bittailor/BtSolarMonitor/Firmware/sketchbook/SolarMonitor/SolarMonitorSettings.default_settings.hpp

Bt::SolarMonitor::MainController::Settings sSettings = {
         {
                  "GprsSimPin",
                  "GprsAccessPointName"
         },
         {
                  "MqttBroker",
                  "MqttDeviceId",
                  "MqttUser",
                  "MqttPassword"
         }
};
