bittailor/BtSolarMonitor/Firmware/sketchbook/SleepAndWakeupWithTC/SleepAndWakeupWithTC.ino

#include <Arduino.h>

// Connect a terminal to Serial (D0/D1), or define this as SerialUSB
#define mySerial Serial

volatile bool TC3_flag = false;
volatile uint32_t tc3_millis = 0;

void configureTC3a();

void setup()
{
    delay(3000);

    pinMode(LED_BUILTIN, OUTPUT);

    mySerial.begin(57600);
    mySerial.println("Startup");

    configureTC3a();

    mySerial.println("Configuration Complete");
}

void loop()
{
    if (TC3_flag) {
        static int counter;
        static uint32_t prev_millis;
        uint32_t my_millis = tc3_millis;
        TC3_flag = false;
        mySerial.println(String("tick, ms: ") + (my_millis - prev_millis) + " " + counter);
        prev_millis = my_millis;
        flashLED();
        if (++counter >= 60) {
            static uint32_t prev_millis;
            mySerial.println(String("Long term tick: ") + (my_millis - prev_millis));
            prev_millis = my_millis;
            counter = 0;
        }
    }
    systemSleep();
}

void flashLED()
{
    static bool led;
    led = !led;                         //flip status led
    if (led) {
        digitalWrite(LED_BUILTIN, LOW);
    }
    else {
        digitalWrite(LED_BUILTIN, HIGH);
    }
}

void systemSleep()
{
    // Set the sleep mode
    SCB->SCR |= SCB_SCR_SLEEPDEEP_Msk;

    if (USB->DEVICE.FSMSTATUS.bit.FSMSTATE == USB_FSMSTATUS_FSMSTATE_SUSPEND_Val) {
        // Disable USB
        USBDevice.detach();

        // SAMD sleep
        __WFI();

        // Enable USB and wait for resume if attached
        USBDevice.attach();
        USB->DEVICE.CTRLB.bit.UPRSM = 0x01u;
        while (USB->DEVICE.CTRLB.bit.UPRSM)
            ;
    }
}

void configureTC3a()
{
    // The GCLK clock provider to use
    // GCLK0, GCLK1 & GCLK3 are used already, see startup.c
    const uint8_t GCLK_SRC = 4;

    // Configure the XOSC32K to run in standby
    SYSCTRL->XOSC32K.bit.RUNSTDBY = 1;

    // Setup clock provider GCLK_SRC with a /2 source divider
    // GCLK_GENDIV_ID(X) specifies which GCLK we are configuring
    // GCLK_GENDIV_DIV(Y) specifies the clock prescalar / divider
    // If GENCTRL.DIVSEL is set (see further below) the divider
    // is 2^(Y+1). If GENCTRL.DIVSEL is 0, the divider is simply Y
    // This register has to be written in a single operation
    GCLK->GENDIV.reg = GCLK_GENDIV_ID(GCLK_SRC) | GCLK_GENDIV_DIV(2);
    while ( GCLK->STATUS.reg & GCLK_STATUS_SYNCBUSY) {
        /* Wait for synchronization */
    }

    // Configure the GCLK module
    // GCLK_GENCTRL_GENEN, enable the specific GCLK module
    // GCLK_GENCTRL_SRC_XOSC32K, set the source to the XOSC32K
    // GCLK_GENCTRL_ID(X), specifies which GCLK we are configuring
    // GCLK_GENCTRL_DIVSEL, specify which prescalar mode we are using
    // GCLK_RUNSTDBY, keep the GCLK running when in standby mode
    // Output from this module is 16khz (32khz / 2)
    // This register has to be written in a single operation.
    GCLK->GENCTRL.reg = GCLK_GENCTRL_GENEN |
            GCLK_GENCTRL_SRC_XOSC32K |
            GCLK_GENCTRL_ID(GCLK_SRC) |
            GCLK_GENCTRL_RUNSTDBY;
    while (GCLK->STATUS.reg & GCLK_STATUS_SYNCBUSY) {
        /* Wait for synchronization */
    }

    // Turn the power to the TC3 module on
    PM->APBCMASK.reg |= PM_APBCMASK_TC3;

    // Set TC3 (shared with TCC2) GCLK source to GCLK_SRC
    // GCLK_CLKCTRL_CLKEN, enable the generic clock
    // GCLK_CLKCTRL_GEN(X), specifies the GCLK generator source
    // GCLK_CLKCTRL_ID(X), specifies which generic clock we are configuring
    GCLK->CLKCTRL.reg = GCLK_CLKCTRL_CLKEN |
            GCLK_CLKCTRL_GEN(GCLK_SRC) |
            GCLK_CLKCTRL_ID(GCM_TCC2_TC3);
    while (GCLK->STATUS.reg & GCLK_STATUS_SYNCBUSY) {
        /* Wait for synchronization */
    }

    // Disable TC3. This is required (if enabled already)
    // before setting certain registers
    TC3->COUNT8.CTRLA.reg &= ~TC_CTRLA_ENABLE;
    while (TC3->COUNT8.STATUS.reg & TC_STATUS_SYNCBUSY) {
        /* Wait for synchronization */
    }

    // Set the mode to 8 bit and set it to run in standby
    // TC_CTRLA_MODE_COUNT8, specify 8bit mode
    // TC_CTRLA_RUNSTDBY, keep the module running when in standby
    // TC_CTRLA_PRESCALER_DIVxx, set the prescalar to 64
    // Prescalar options include: DIV1, DIV2, DIV4, DIV8,
    // DIV16, DIV64, DIV256, DIV1024
    TC3->COUNT8.CTRLA.reg = TC_CTRLA_MODE_COUNT8 |
            TC_CTRLA_RUNSTDBY |
            TC_CTRLA_PRESCALER_DIV64;
    while (TC3->COUNT8.STATUS.reg & TC_STATUS_SYNCBUSY) {
        /* Wait for synchronization */
    }

    // Enable interrupt on overflow
    // TC_INTENSET_OVF, enable an interrupt on overflow
    TC3->COUNT8.INTENSET.reg = TC_INTENSET_OVF;
    while (TC3->COUNT8.STATUS.reg & TC_STATUS_SYNCBUSY) {
        /* Wait for synchronization */
    }

    // Enable TC3
    TC3->COUNT8.CTRLA.reg |= TC_CTRLA_ENABLE;
    while (TC3->COUNT8.STATUS.reg & TC_STATUS_SYNCBUSY) {
        /* Wait for synchronization */
    }

    // Enable the TC3 interrupt vector
    // Set the priority to max
    NVIC_EnableIRQ(TC3_IRQn);
    NVIC_SetPriority(TC3_IRQn, 0x00);
}

// TC3 ISR
void TC3_Handler()
{
    if (TC3->COUNT8.INTFLAG.bit.OVF) {
        tc3_millis = millis();

        // Reset interrupt flag
        TC3->COUNT8.INTFLAG.bit.OVF = 1;

        // Set compare match flag for CC0
        TC3_flag = true;
    }
}
