bittailor/BtSolarMonitor/Firmware/sketchbook/Spike_GprsModule/Spike_GprsModule_Settings.default_settings.hpp

Bt::Net::Gprs::GprsModule::Settings sGprsModuleSettings {
   "SimPin",
   "AccessPointName"
};

#define MQTT_BROKER "broker.shiftr.io"
#define MQTT_CLIENT_ID "A"
#define MQTT_USERNAME "B"
#define MQTT_PASSWORD "C"
